Figra2406/Grupo-1-FunBio/Documentos/Entregable 8/Entregable N°8.pdf

### FUNDAMENTOS DE BIODISEÑO

Entrega N°8:
Diseño esquemático del prototipo. Modelado 3D de los elementos que conforman el prototipo

Grupo 1

Integrantes:
Fabrizzio Marcel Céliz Gálvez Jhogger Cercado Limay
Ximena Gema Palomino Cusi
Flavia Sharick Tasayco Cueva Javier Denis Bernal Garayar Lucero Rubi Cercado Medina 26/05/26

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
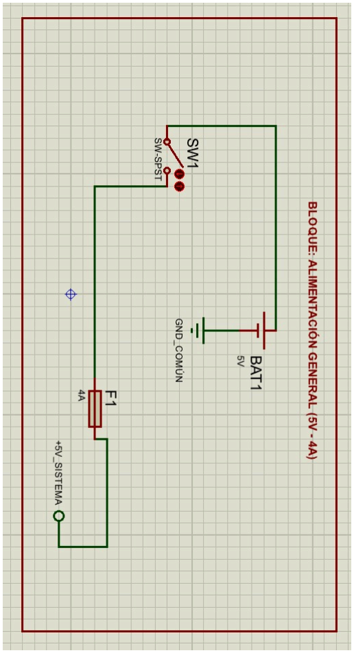
[picture p11: figure]
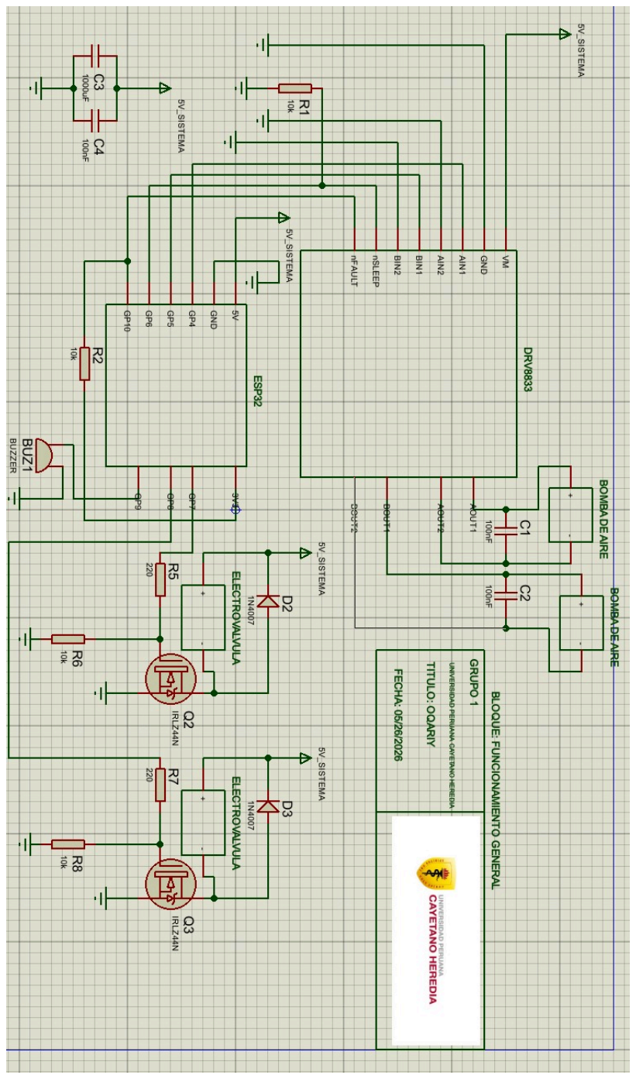
[picture p12: page 3]

- Modelado 3D de los componentes por separado

Enlace:
https://cad.onshape.com/documents/be2a5b314c4f87f89ed8f853/w/25158f458f5c1d92be45dfe7/e/40a314e245f769cd47d0e264 (https://cad.onshape.com/documents/be2a5b314c4f87f89ed8f853/w/25158f458f5c1d92be45dfe7/e/40a314e245f769cd47d0e264)
1. Bateria recargable 6v 3000mA
2. ESP32

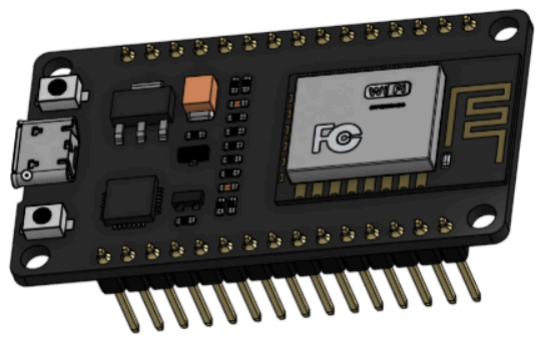
[picture p13: figure]

3. Mini bomba de aire 6V

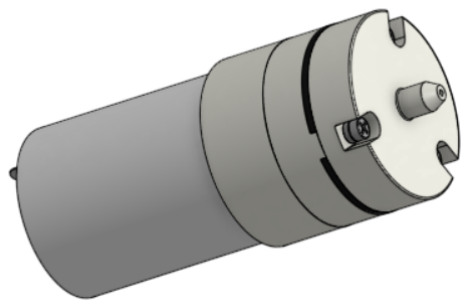
[picture p14: figure]

4. Micro valvula solenoide electrica

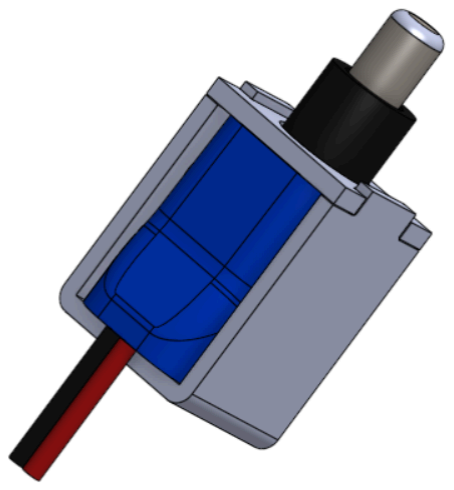
[picture p15: figure]

5. DRV8833

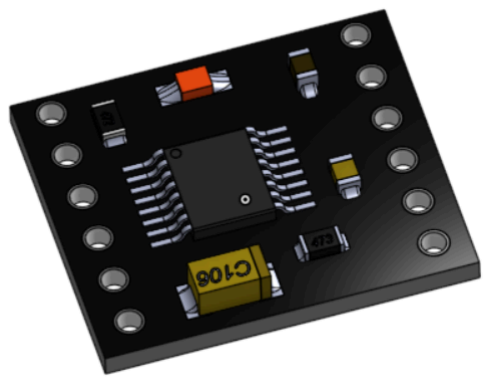
[picture p16: figure]

6. Transistor electronico MOSFET

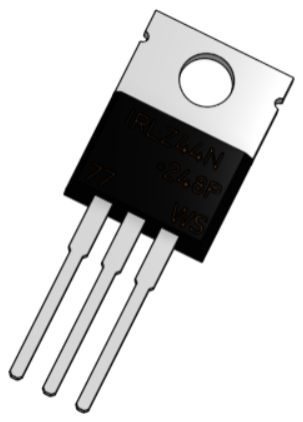
[picture p17: figure]

7. Buzzer

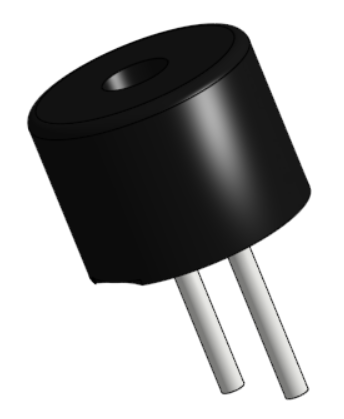
[picture p18: figure]

8. Bolsa de aire

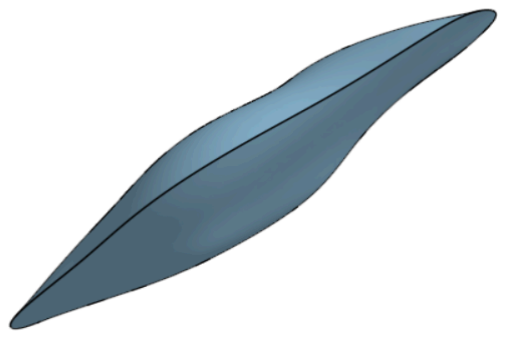
[picture p19: figure]

9. Soporte de elevación

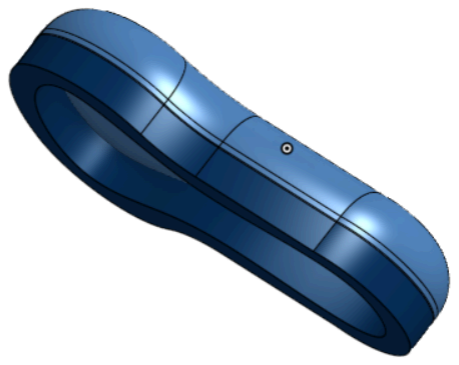
[picture p20: figure]
