Figra2406/Grupo-1-FunBio/Taller de modelado 3D/Lucero Cercado Medina/lucero-rubi-cercado-medina-7954d3f0-f888-4501-aeab-b428a17639e1-certificate.pdf

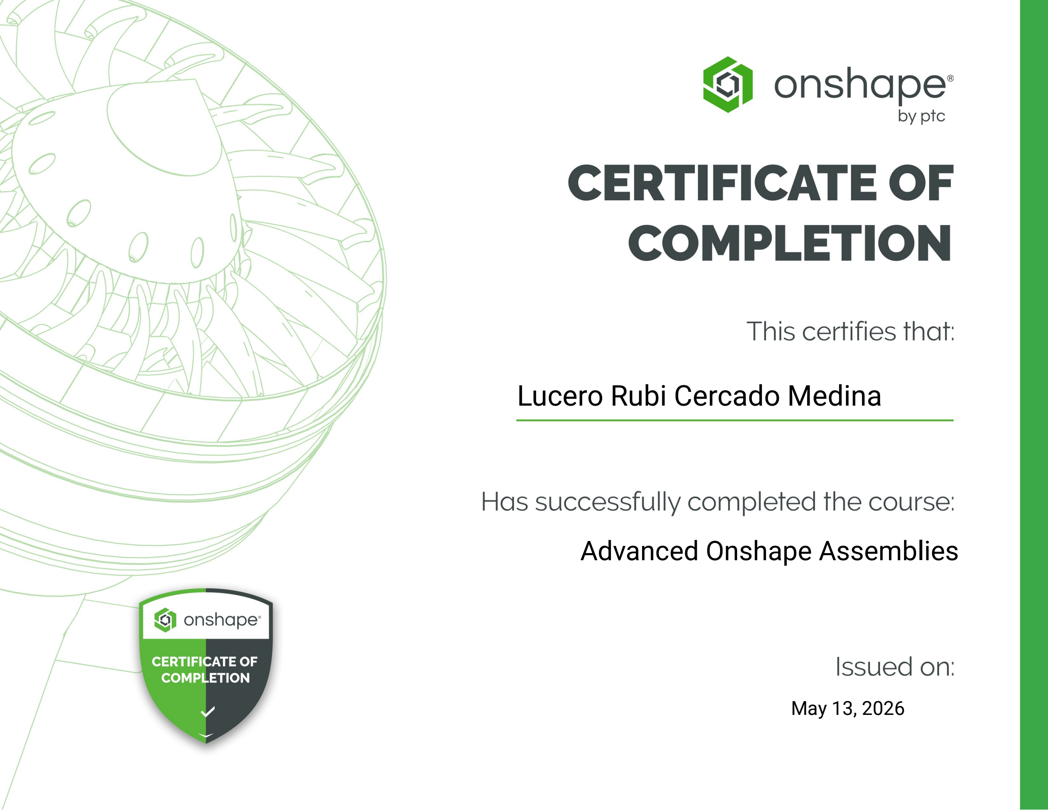
[picture p21: page 1]

Lucero Rubi Cercado Medina

Advanced Onshape Assemblies

May 13, 2026
