Figra2406/Grupo-1-FunBio/Taller de modelado 3D/Javier Bernal Garay/javier-bernal-1c711cbe-b023-4eb5-af85-3679d9fcc2b4-certificate.pdf

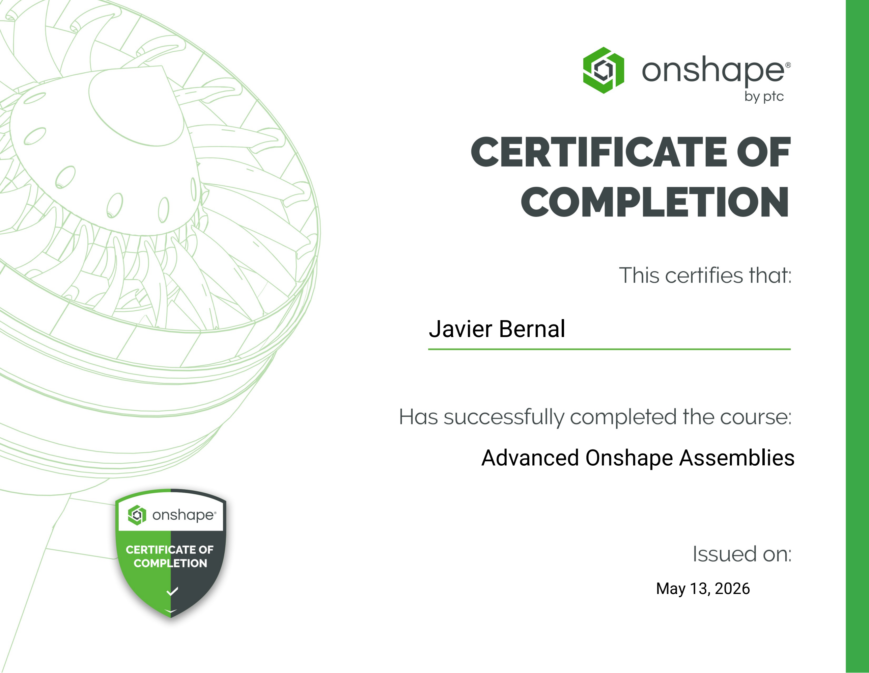
[picture p22: page 1]

Javier Bernal

Advanced Onshape Assemblies

May 13, 2026
