Figra2406/Grupo-1-FunBio/Taller de modelado 3D/Javier Bernal Garay/javier-bernal-4c75c975-a74c-4049-8172-a8e1c8366483-certificate.pdf

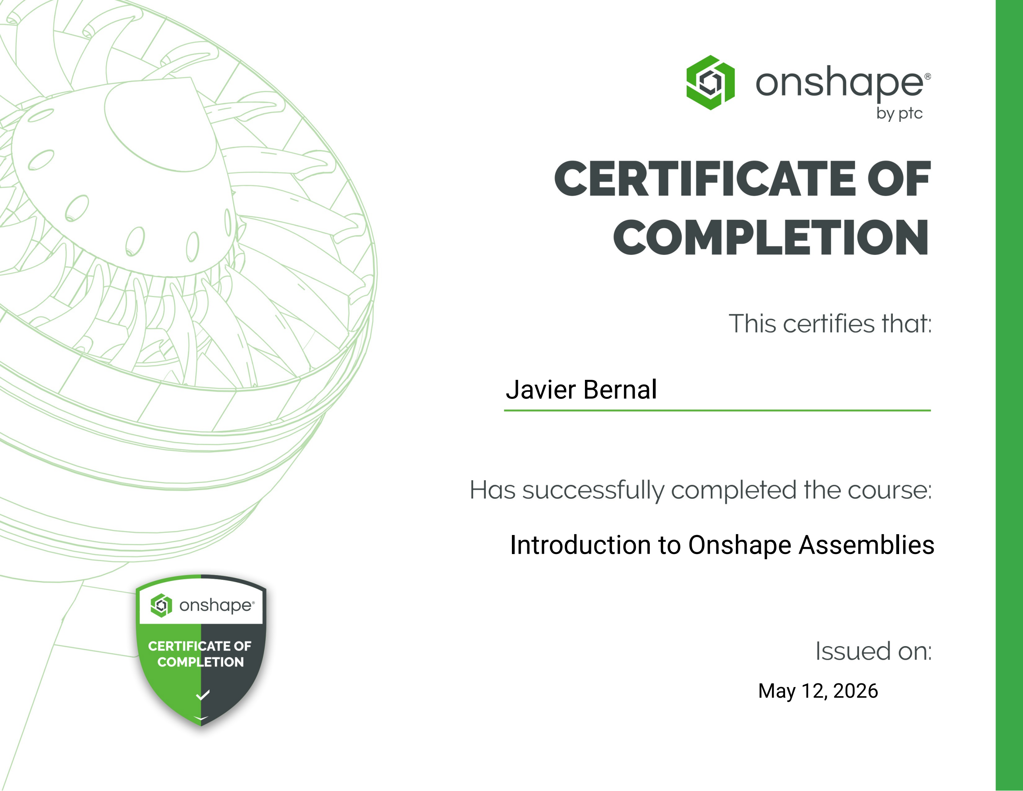
[picture p23: page 1]

Javier Bernal

May 12, 2026

Introduction to Onshape Assemblies
