Figra2406/Grupo-1-FunBio/Taller de modelado 3D/Lucero Cercado Medina/de60d86d-8ce0-4c51-bb0f-3838b6e36f22-lucero-rubi-cercado-medina-431d9740-cd10-450a-8145-1995c47c14eb-certificate.pdf

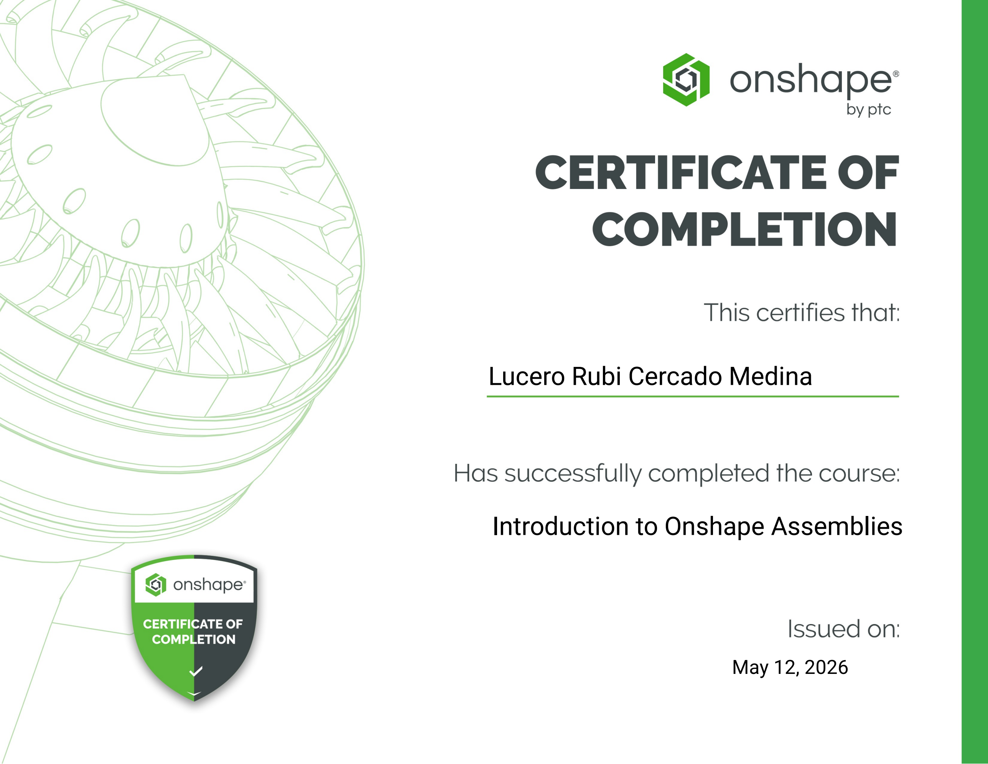
[picture p24: page 1]

Lucero Rubi Cercado Medina

May 12, 2026

Introduction to Onshape Assemblies
