Figra2406/Grupo-1-FunBio/Taller de modelado 3D/Ximena Palomino Cusi/gema-palomino-905db795-45b4-4cf6-ba11-d0b69c7ab82a-certificate.pdf

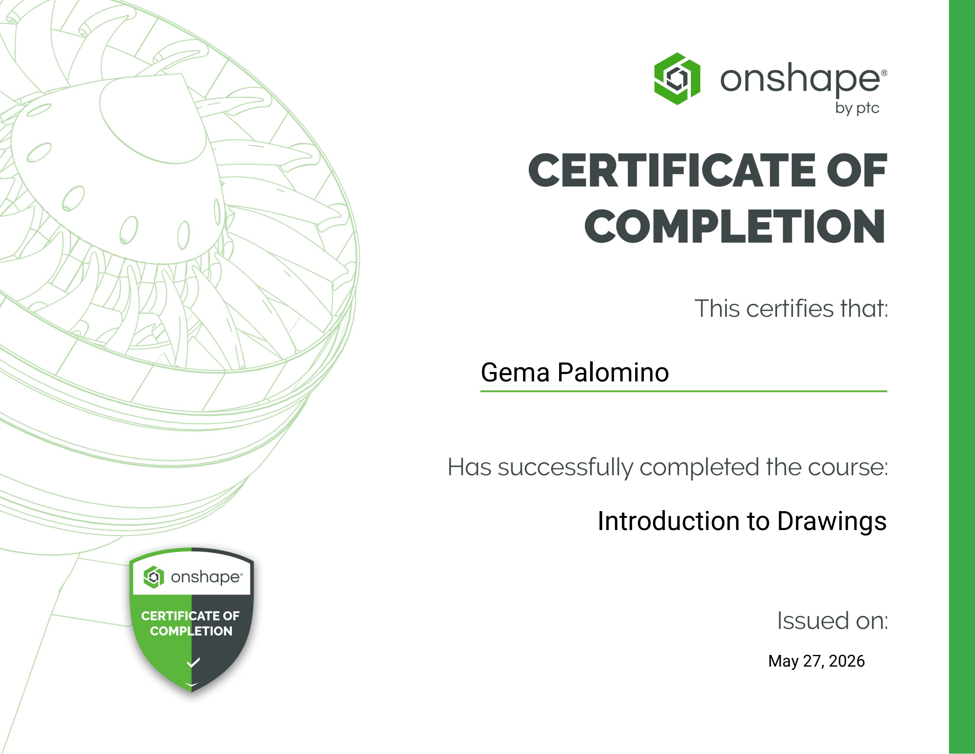
[picture p25: page 1]

Gema Palomino

May 27, 2026

Introduction to Drawings
