Figra2406/Grupo-1-FunBio/Taller de modelado 3D/Flavia Tasayco Cueva/Detailed Drawings.pdf

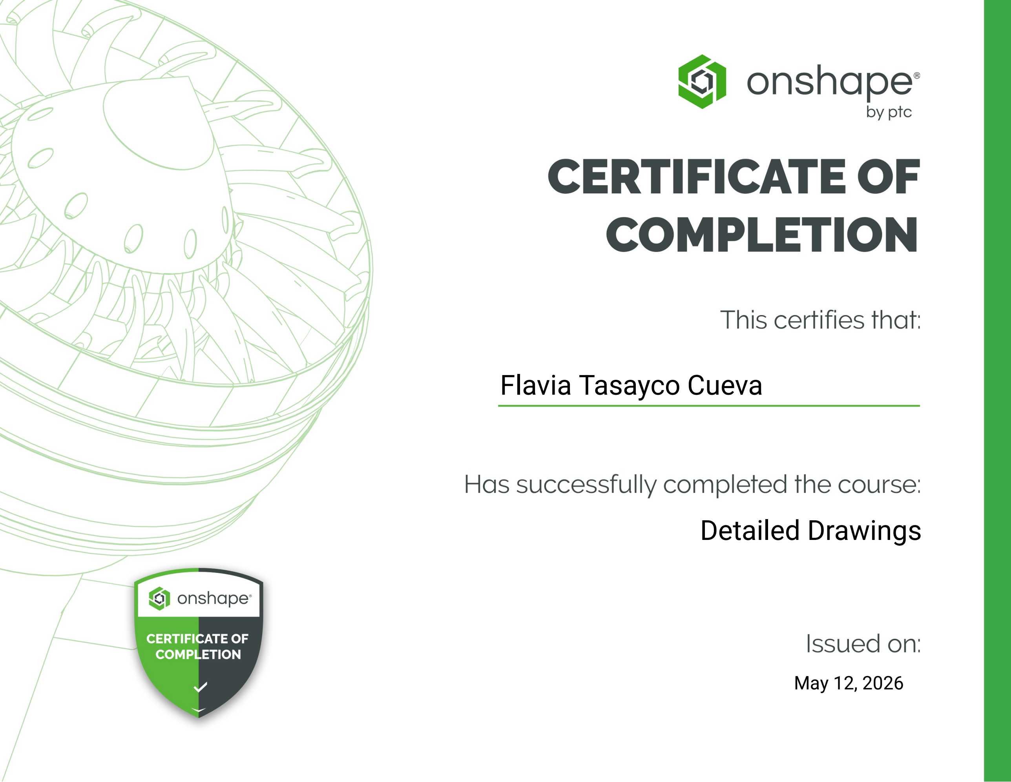
[picture p26: page 1]

Flavia Tasayco Cueva

May 12, 2026

Detailed Drawings
