Figra2406/Grupo-1-FunBio/Taller de modelado 3D/Javier Bernal Garay/javier-bernal-8e3854ba-d66e-4511-bbd3-1ceb8dc3e522-certificate.pdf

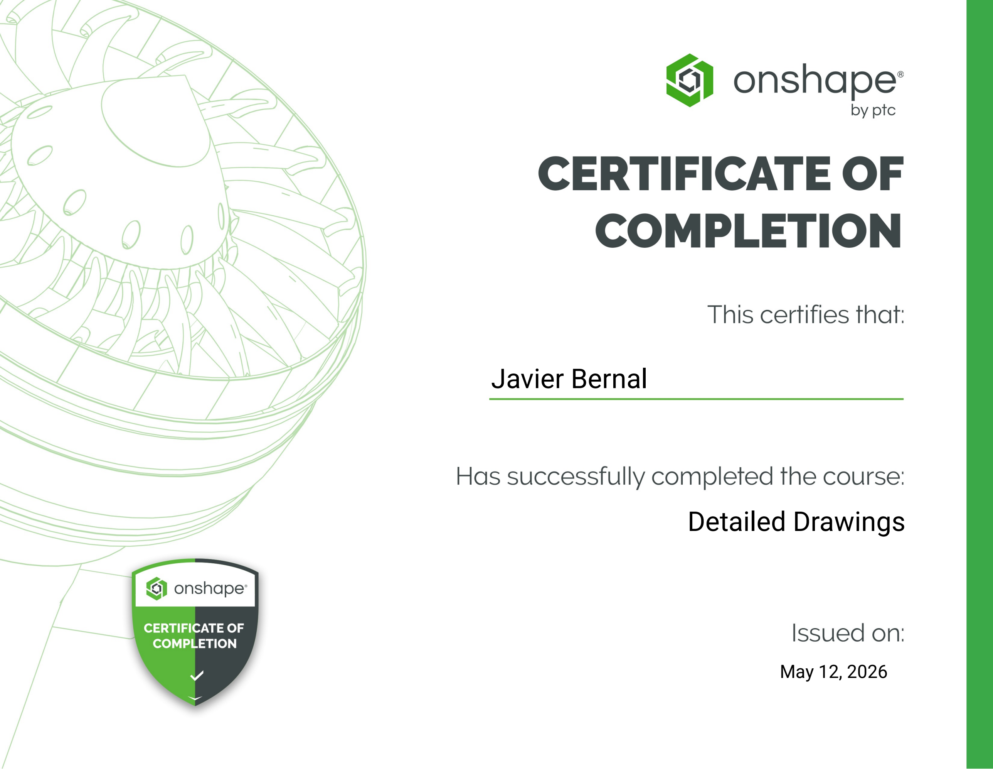
[picture p27: page 1]

Javier Bernal

May 12, 2026

Detailed Drawings
