Figra2406/Grupo-1-FunBio/Taller de modelado 3D/Lucero Cercado Medina/de60d86d-8ce0-4c51-bb0f-3838b6e36f22-lucero-rubi-cercado-medina-5331641c-7917-43de-a894-fe1695d6f287-certificate.pdf

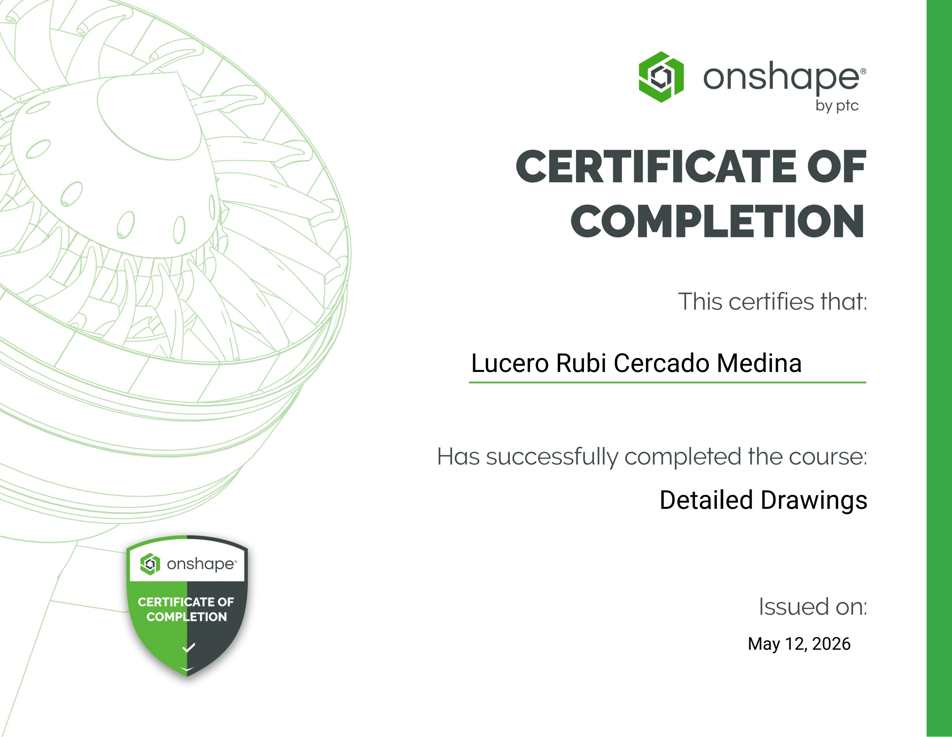
[picture p28: page 1]

Lucero Rubi Cercado Medina

May 12, 2026

Detailed Drawings
