Figra2406/Grupo-1-FunBio/Taller de modelado 3D/Ximena Palomino Cusi/Detailed Drawings.pdf

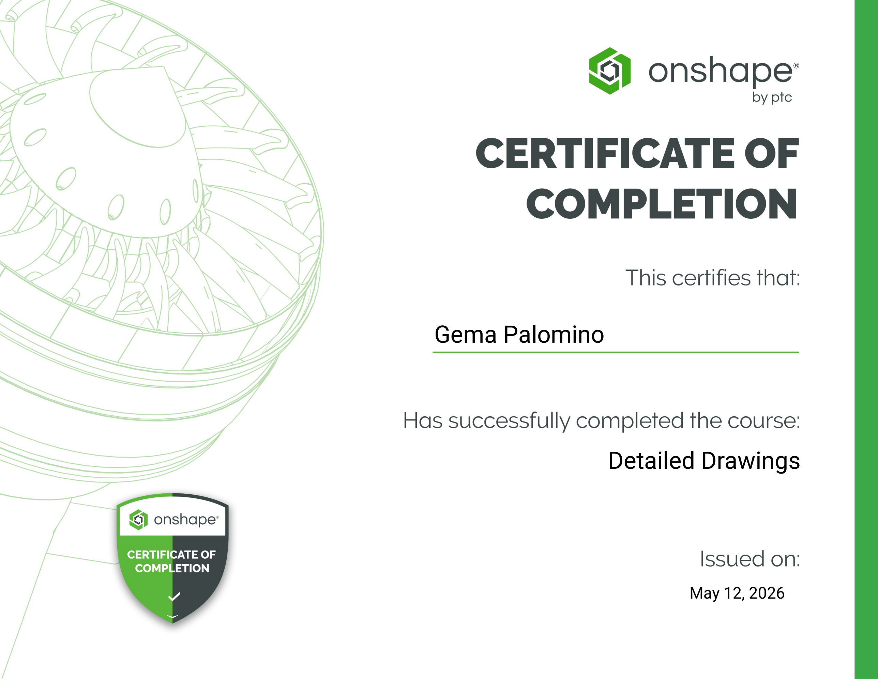
[picture p29: page 1]

Gema Palomino

May 12, 2026

Detailed Drawings
