Figra2406/Grupo-1-FunBio/Taller de modelado 3D/Javier Bernal Garay/javier-bernal-89edafed-4be2-4a4e-a87d-024590466d2e-certificate.pdf

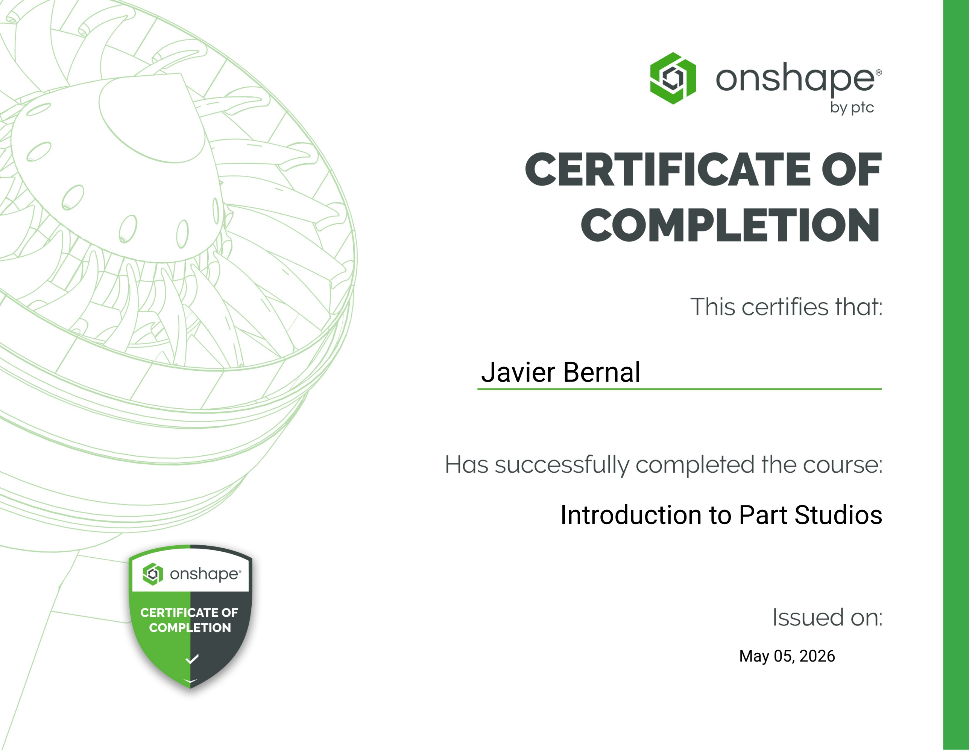
[picture p36: page 1]

Javier Bernal

Introduction to Part Studios

May 05, 2026
