Figra2406/Grupo-1-FunBio/Taller de modelado 3D/Javier Bernal Garay/javier-bernal-d9db2dbc-3374-4bca-a5cd-d3212916cf07-certificate.pdf

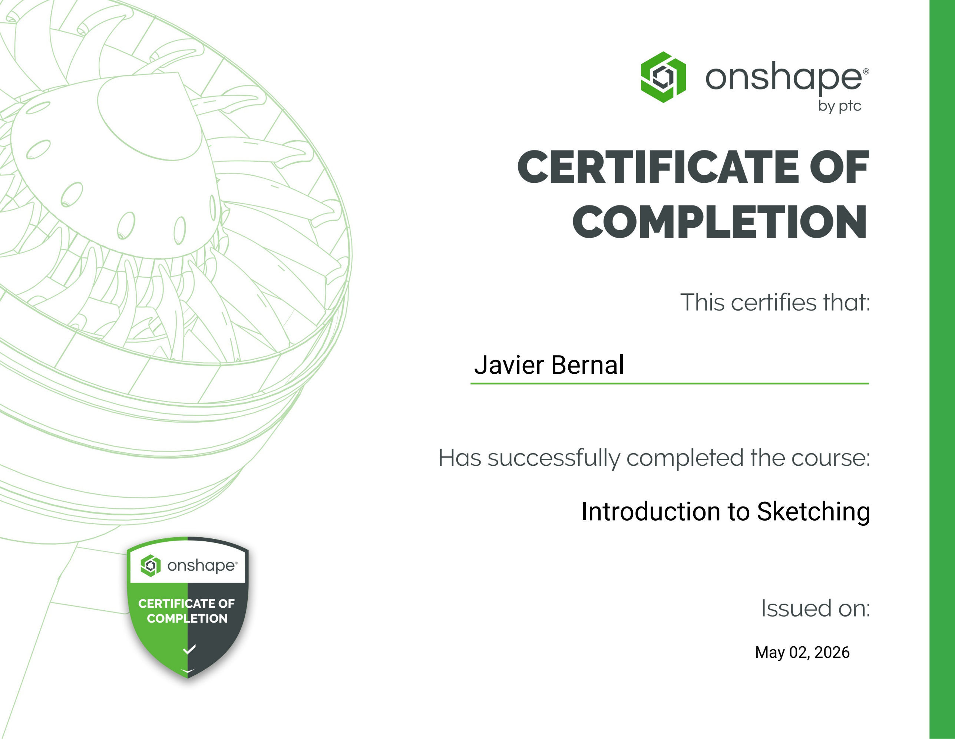
[picture p37: page 1]

Javier Bernal

Introduction to Sketching

May 02, 2026
