Figra2406/Grupo-1-FunBio/Taller de modelado 3D/Flavia Tasayco Cueva/Introduction to Part Studios.Flavia.pdf

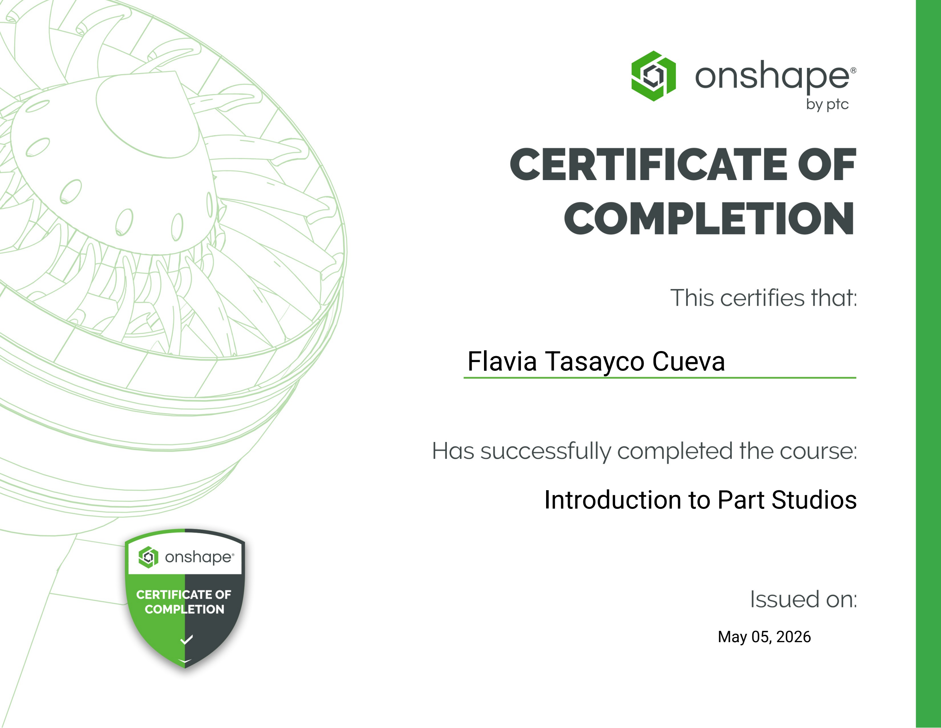
[picture p38: page 1]

Flavia Tasayco Cueva

Introduction to Part Studios

May 05, 2026
