Figra2406/Grupo-1-FunBio/Taller de modelado 3D/Flavia Tasayco Cueva/Introduction to sketching.Flavia.pdf

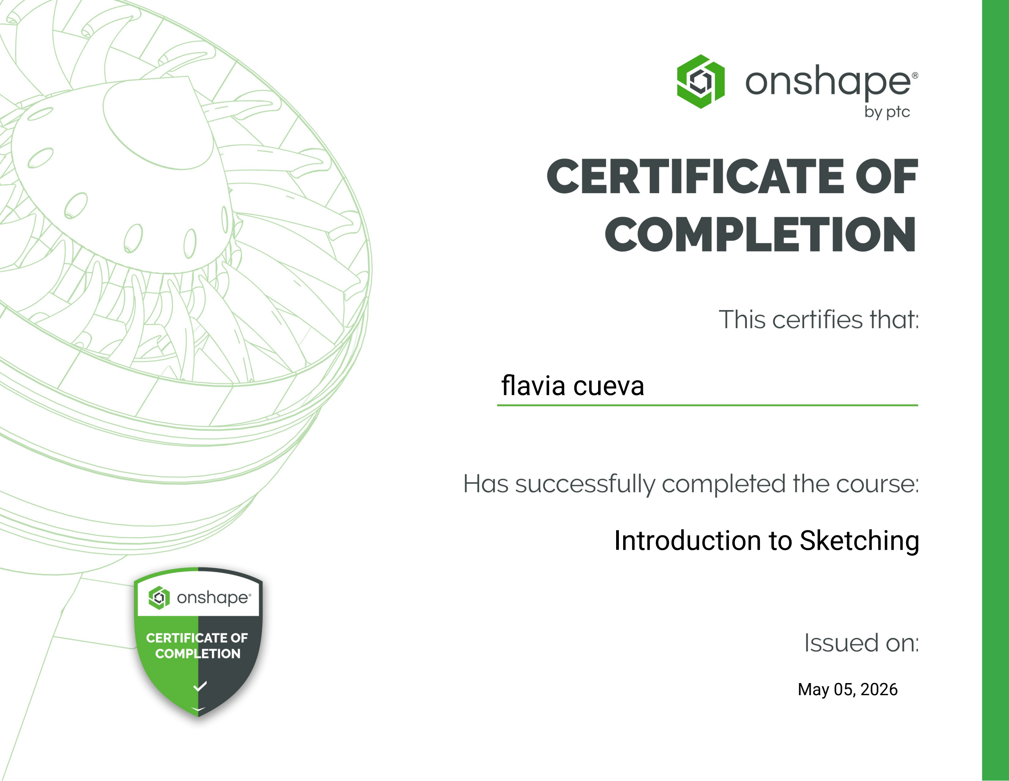
[picture p39: page 1]

avia cueva

Introduction to Sketching

May 05, 2026
