Figra2406/Grupo-1-FunBio/Taller de modelado 3D/Lucero Cercado Medina/lucero-rubi-cercado-medina-7111d44b-160b-4e92-bb52-a8f6cbea0b17-certificate.pdf

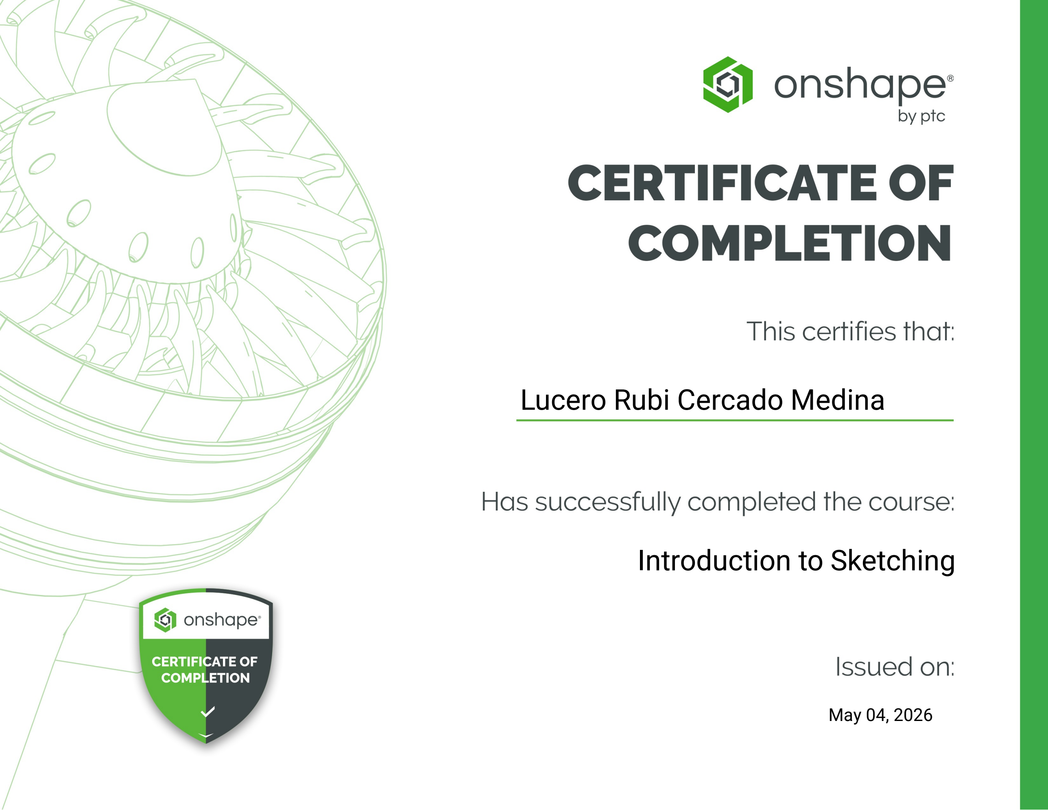
[picture p40: page 1]

Lucero Rubi Cercado Medina

Introduction to Sketching

May 04, 2026
