Figra2406/Grupo-1-FunBio/Taller de modelado 3D/Lucero Cercado Medina/lucero-rubi-cercado-medina-b66944c8-f012-4613-a5c3-b3f6f3d40ffe-certificate.pdf

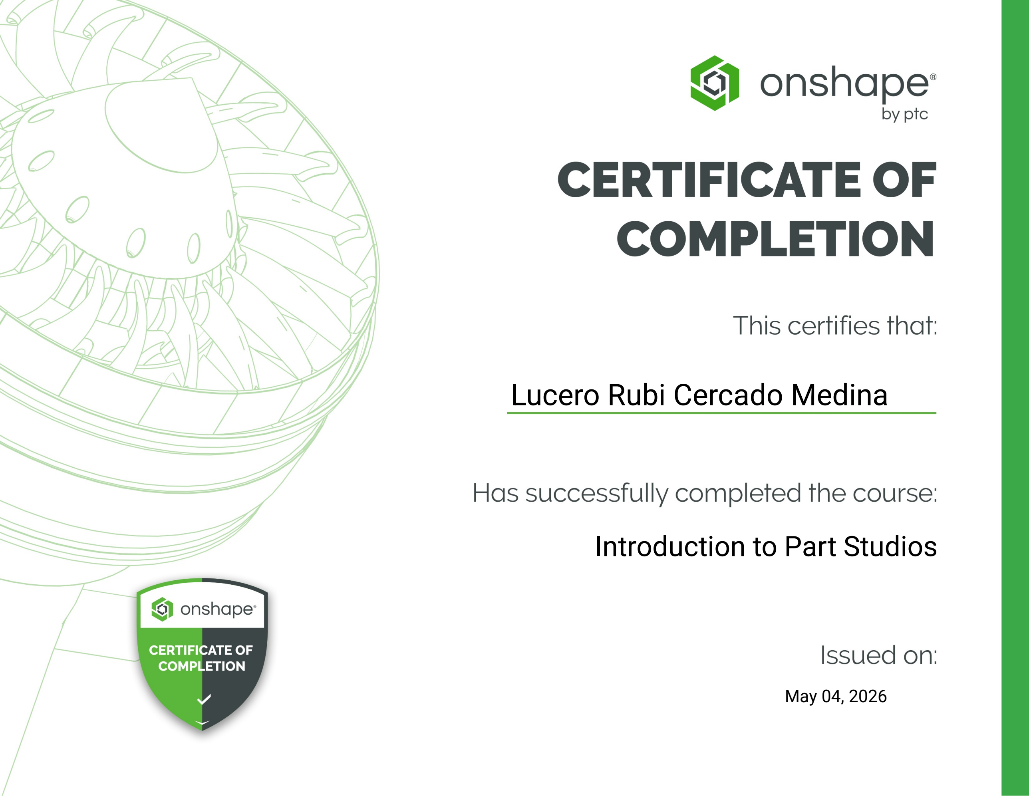
[picture p41: page 1]

Lucero Rubi Cercado Medina

Introduction to Part Studios

May 04, 2026
