Figra2406/Grupo-1-FunBio/Taller de modelado 3D/Ximena Palomino Cusi/Introduction to Part Studios.pdf

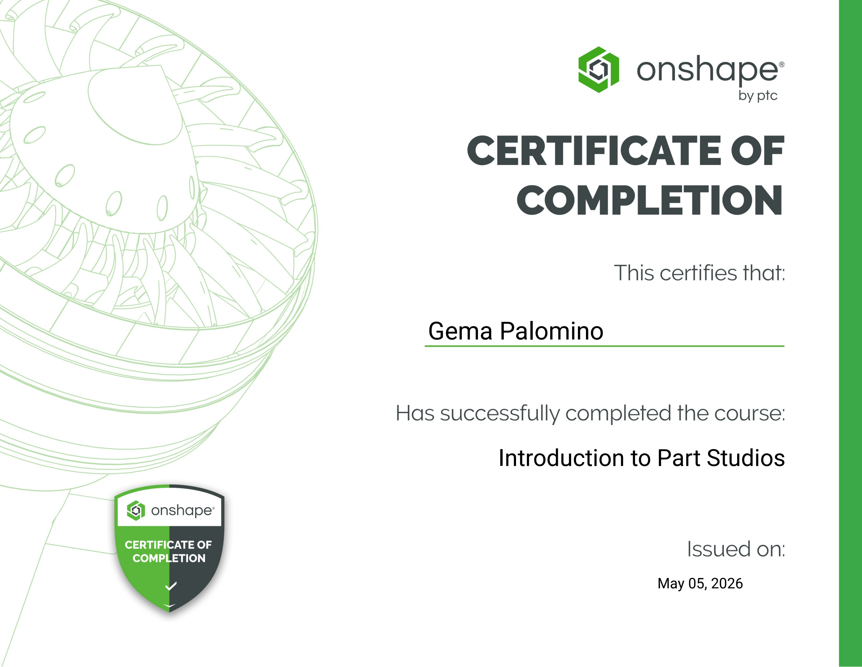
[picture p42: page 1]

Gema Palomino

Introduction to Part Studios

May 05, 2026
