Figra2406/Grupo-1-FunBio/Taller de modelado 3D/Ximena Palomino Cusi/Introducción al dibujo técnico.pdf

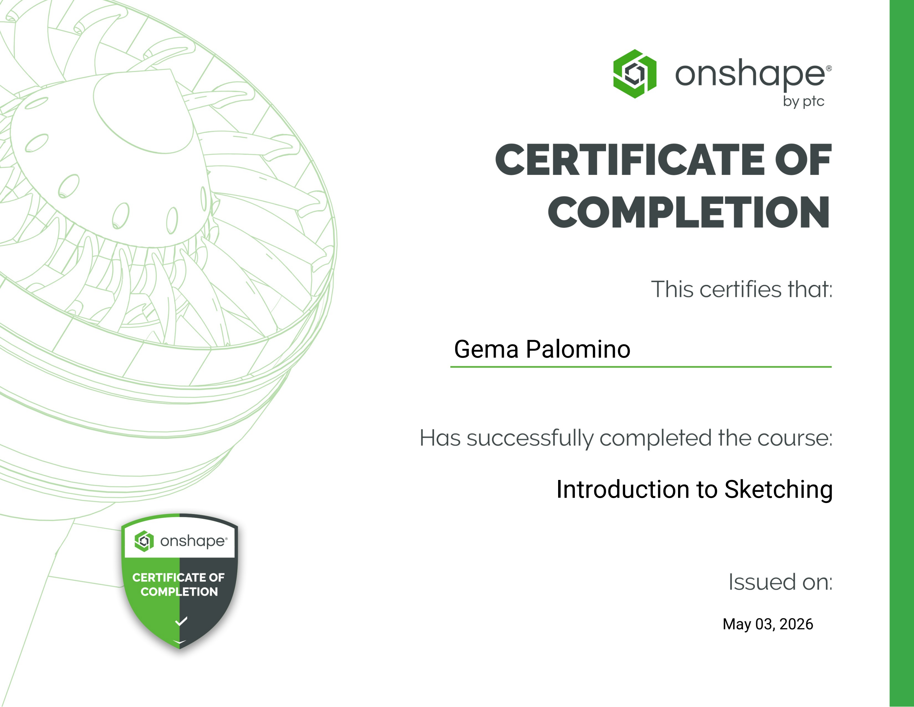
[picture p43: page 1]

Gema Palomino

Introduction to Sketching

May 03, 2026
