Figra2406/Grupo-1-FunBio/Taller de modelado 3D/Jhogger Cercado Limay/Dibujos detallados.pdf

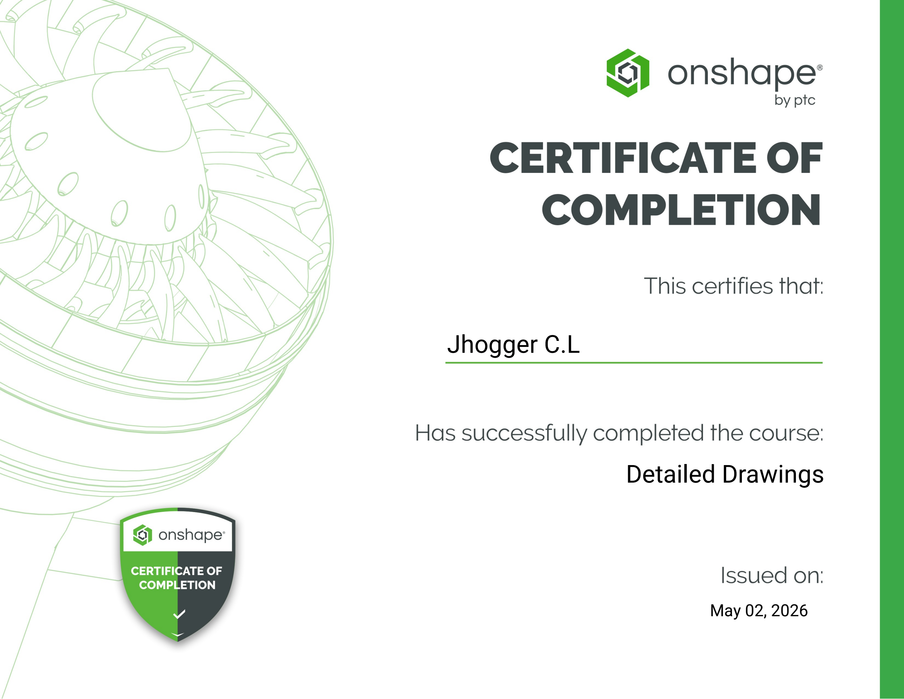
[picture p44: page 1]

Jhogger C.L

May 02, 2026

Detailed Drawings
