Figra2406/Grupo-1-FunBio/Taller de modelado 3D/Jhogger Cercado Limay/Introducción a Part Studios.pdf

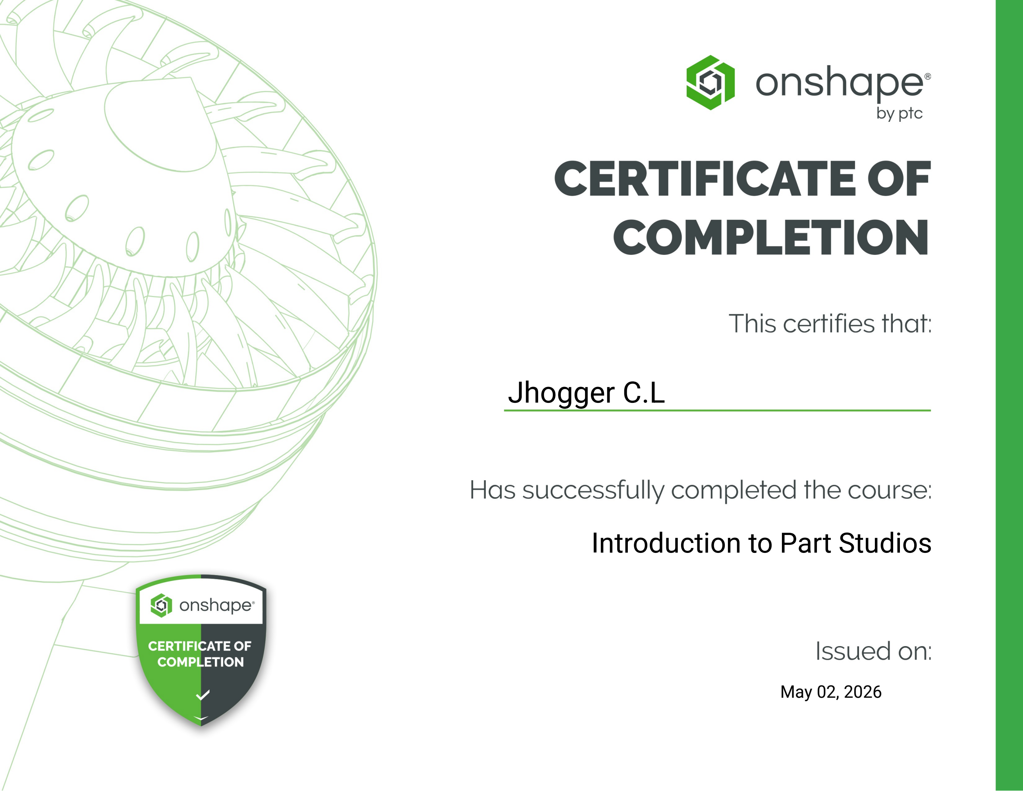
[picture p45: page 1]

Jhogger C.L

Introduction to Part Studios

May 02, 2026
