Figra2406/Grupo-1-FunBio/Taller de modelado 3D/Jhogger Cercado Limay/Introducción al dibujo técnico.pdf

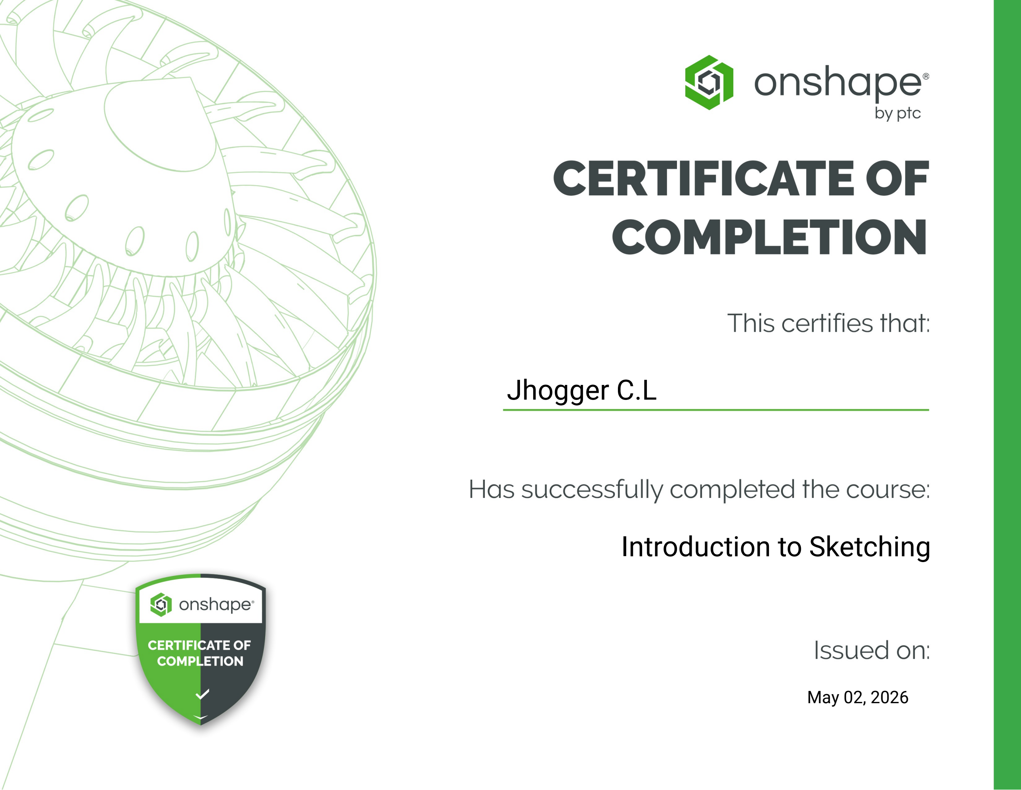
[picture p46: page 1]

Jhogger C.L

Introduction to Sketching

May 02, 2026
