Figra2406/Grupo-1-FunBio/Taller de modelado 3D/Fabrizzio Céliz Gálvez/Introducción a Part Studios Fabrizzio Céliz.pdf

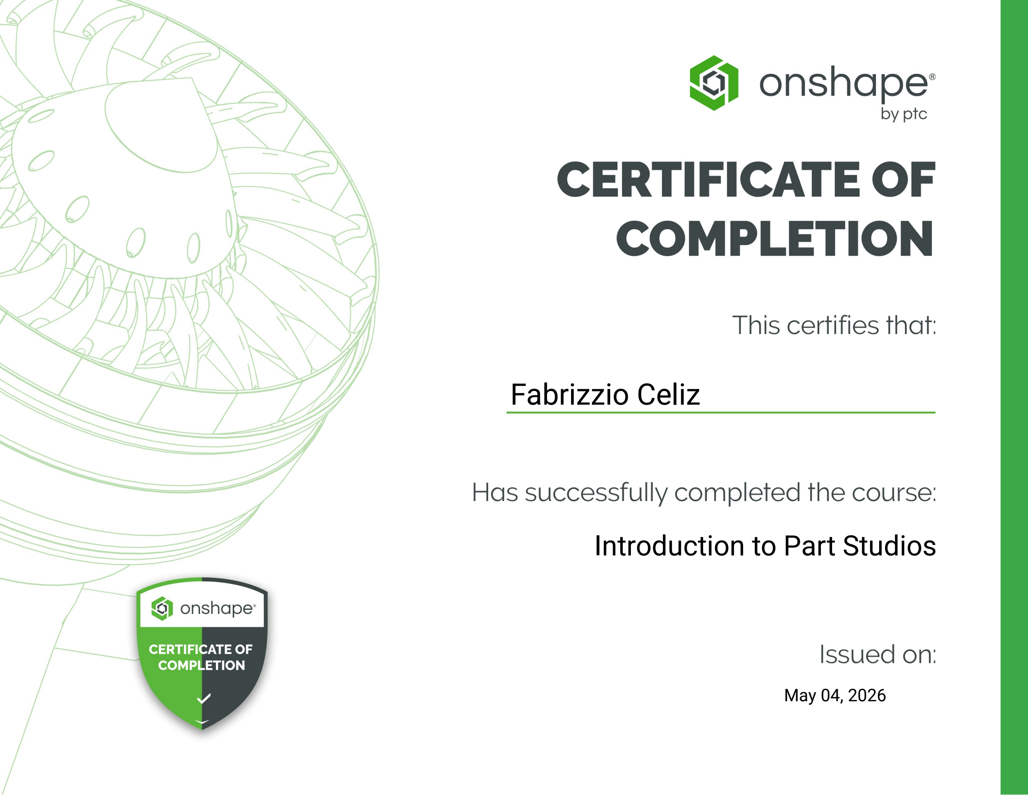
[picture p47: page 1]

Fabrizzio Celiz

Introduction to Part Studios

May 04, 2026
