Figra2406/Grupo-1-FunBio/Taller de modelado 3D/Fabrizzio Céliz Gálvez/Introducción al Dibujo Tecnico Fabrizzio Céliz.pdf

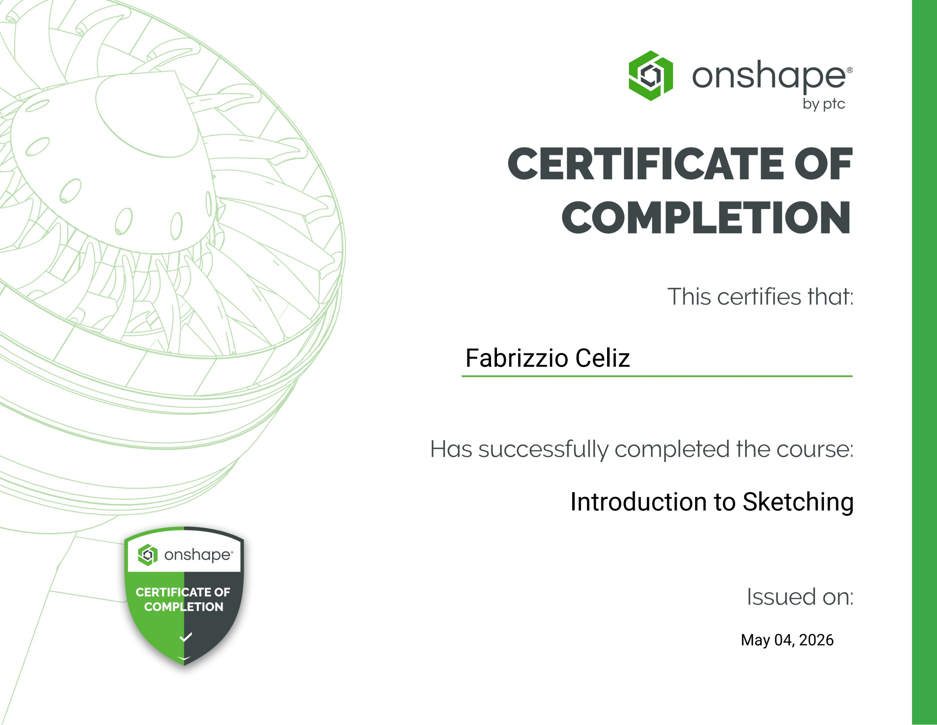
[picture p48: page 1]

Fabrizzio Celiz

Introduction to Sketching

May 04, 2026
