Figra2406/Grupo-1-FunBio/Imagenes/IMG_7878.jpeg

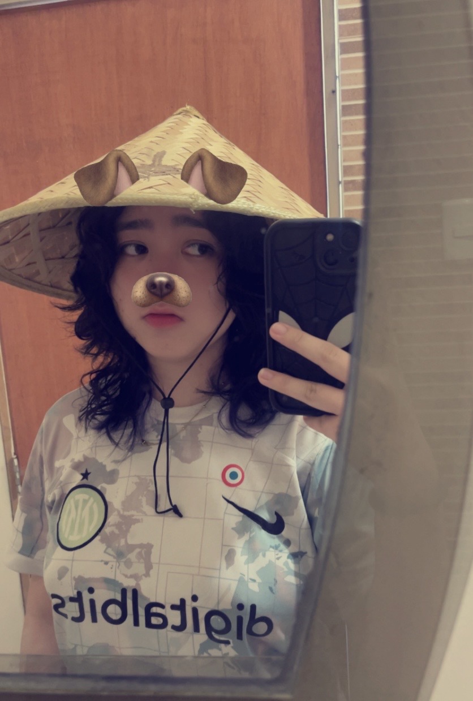
Imagenes/IMG_7878.jpeg
