Figra2406/Grupo-1-FunBio/Documentos/Entregable 9/Riñon plano.pdf

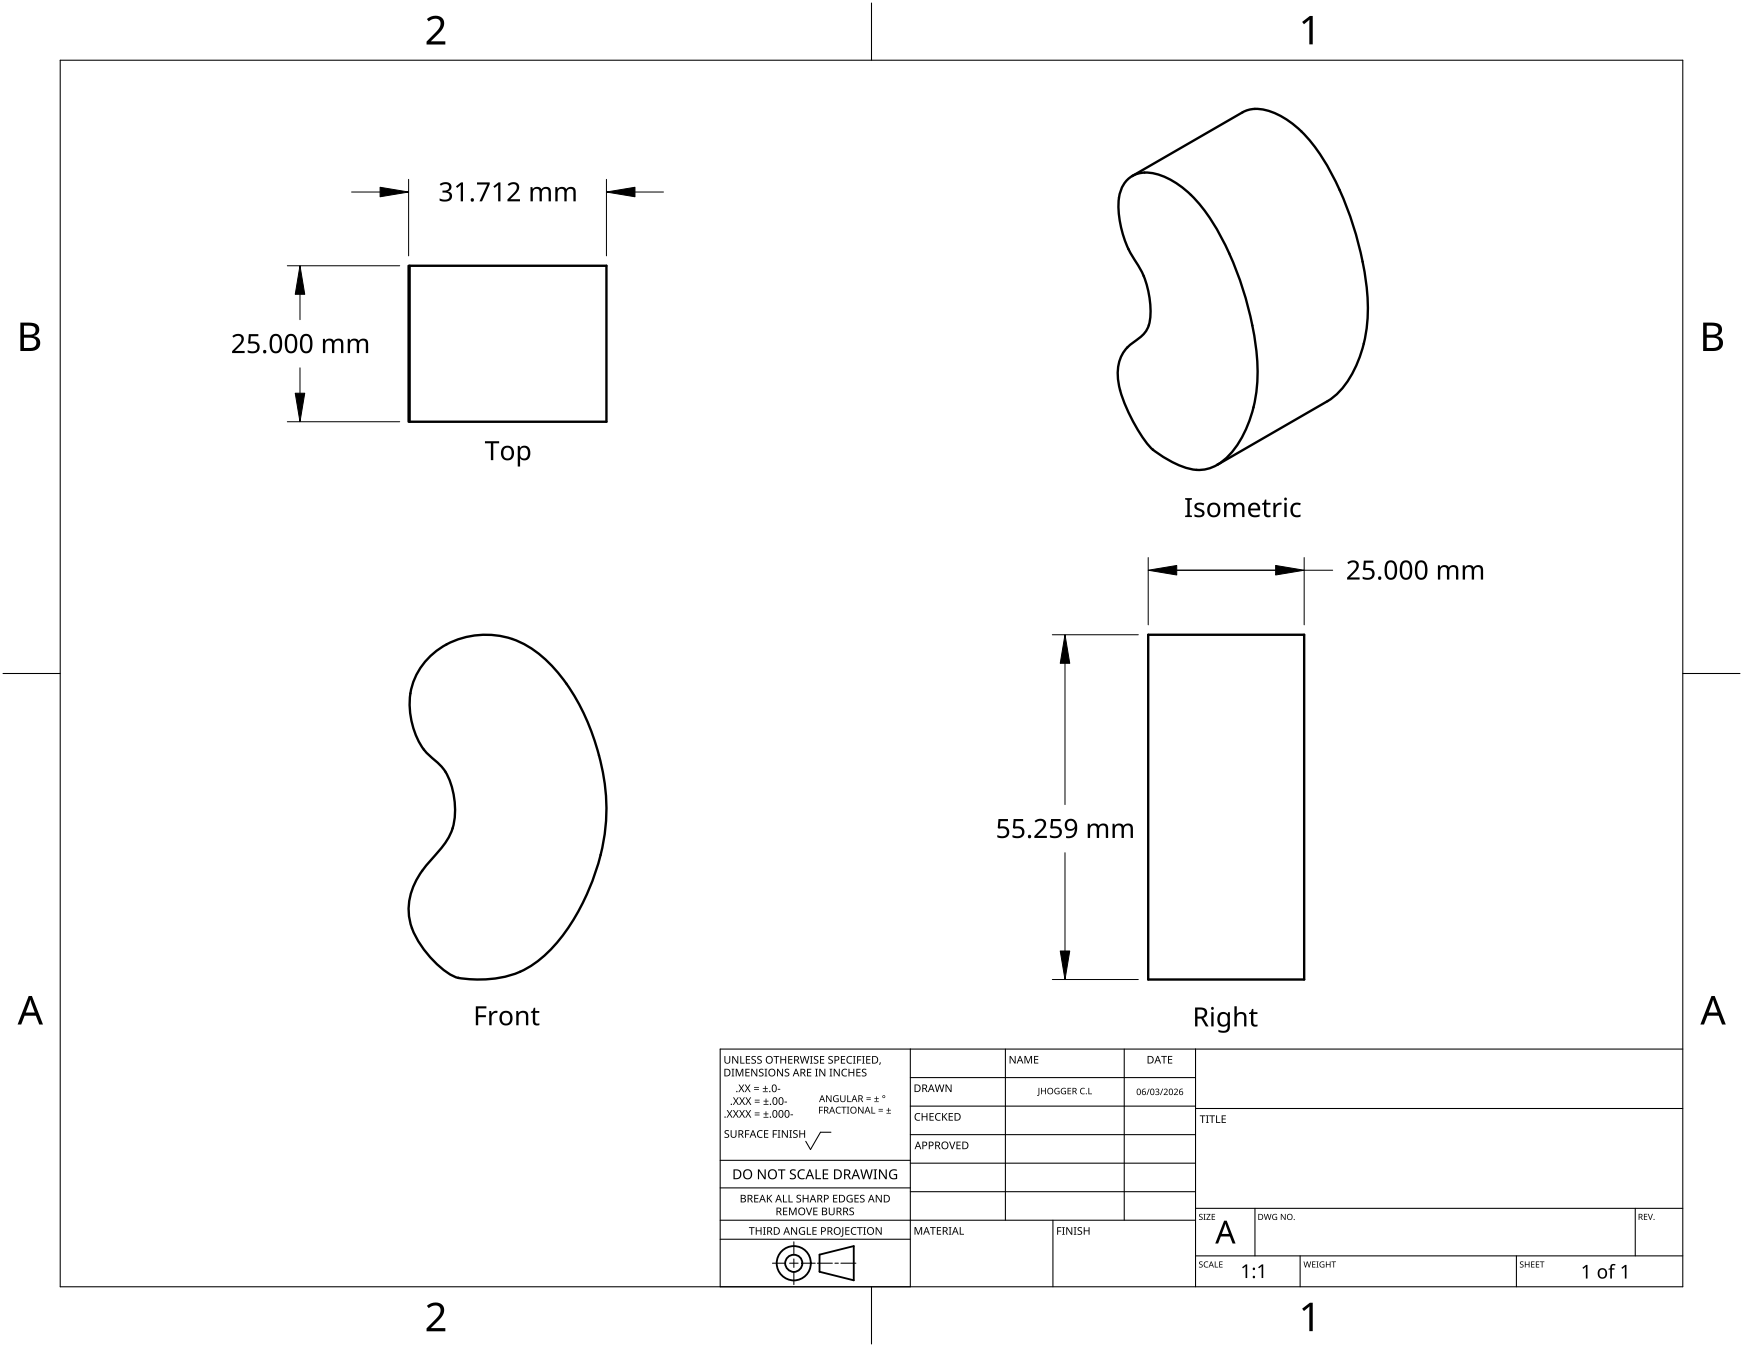
[picture p76: page 1]
