Figra2406/Grupo-1-FunBio/Documentos/Entregable 9/Tapa plano.pdf

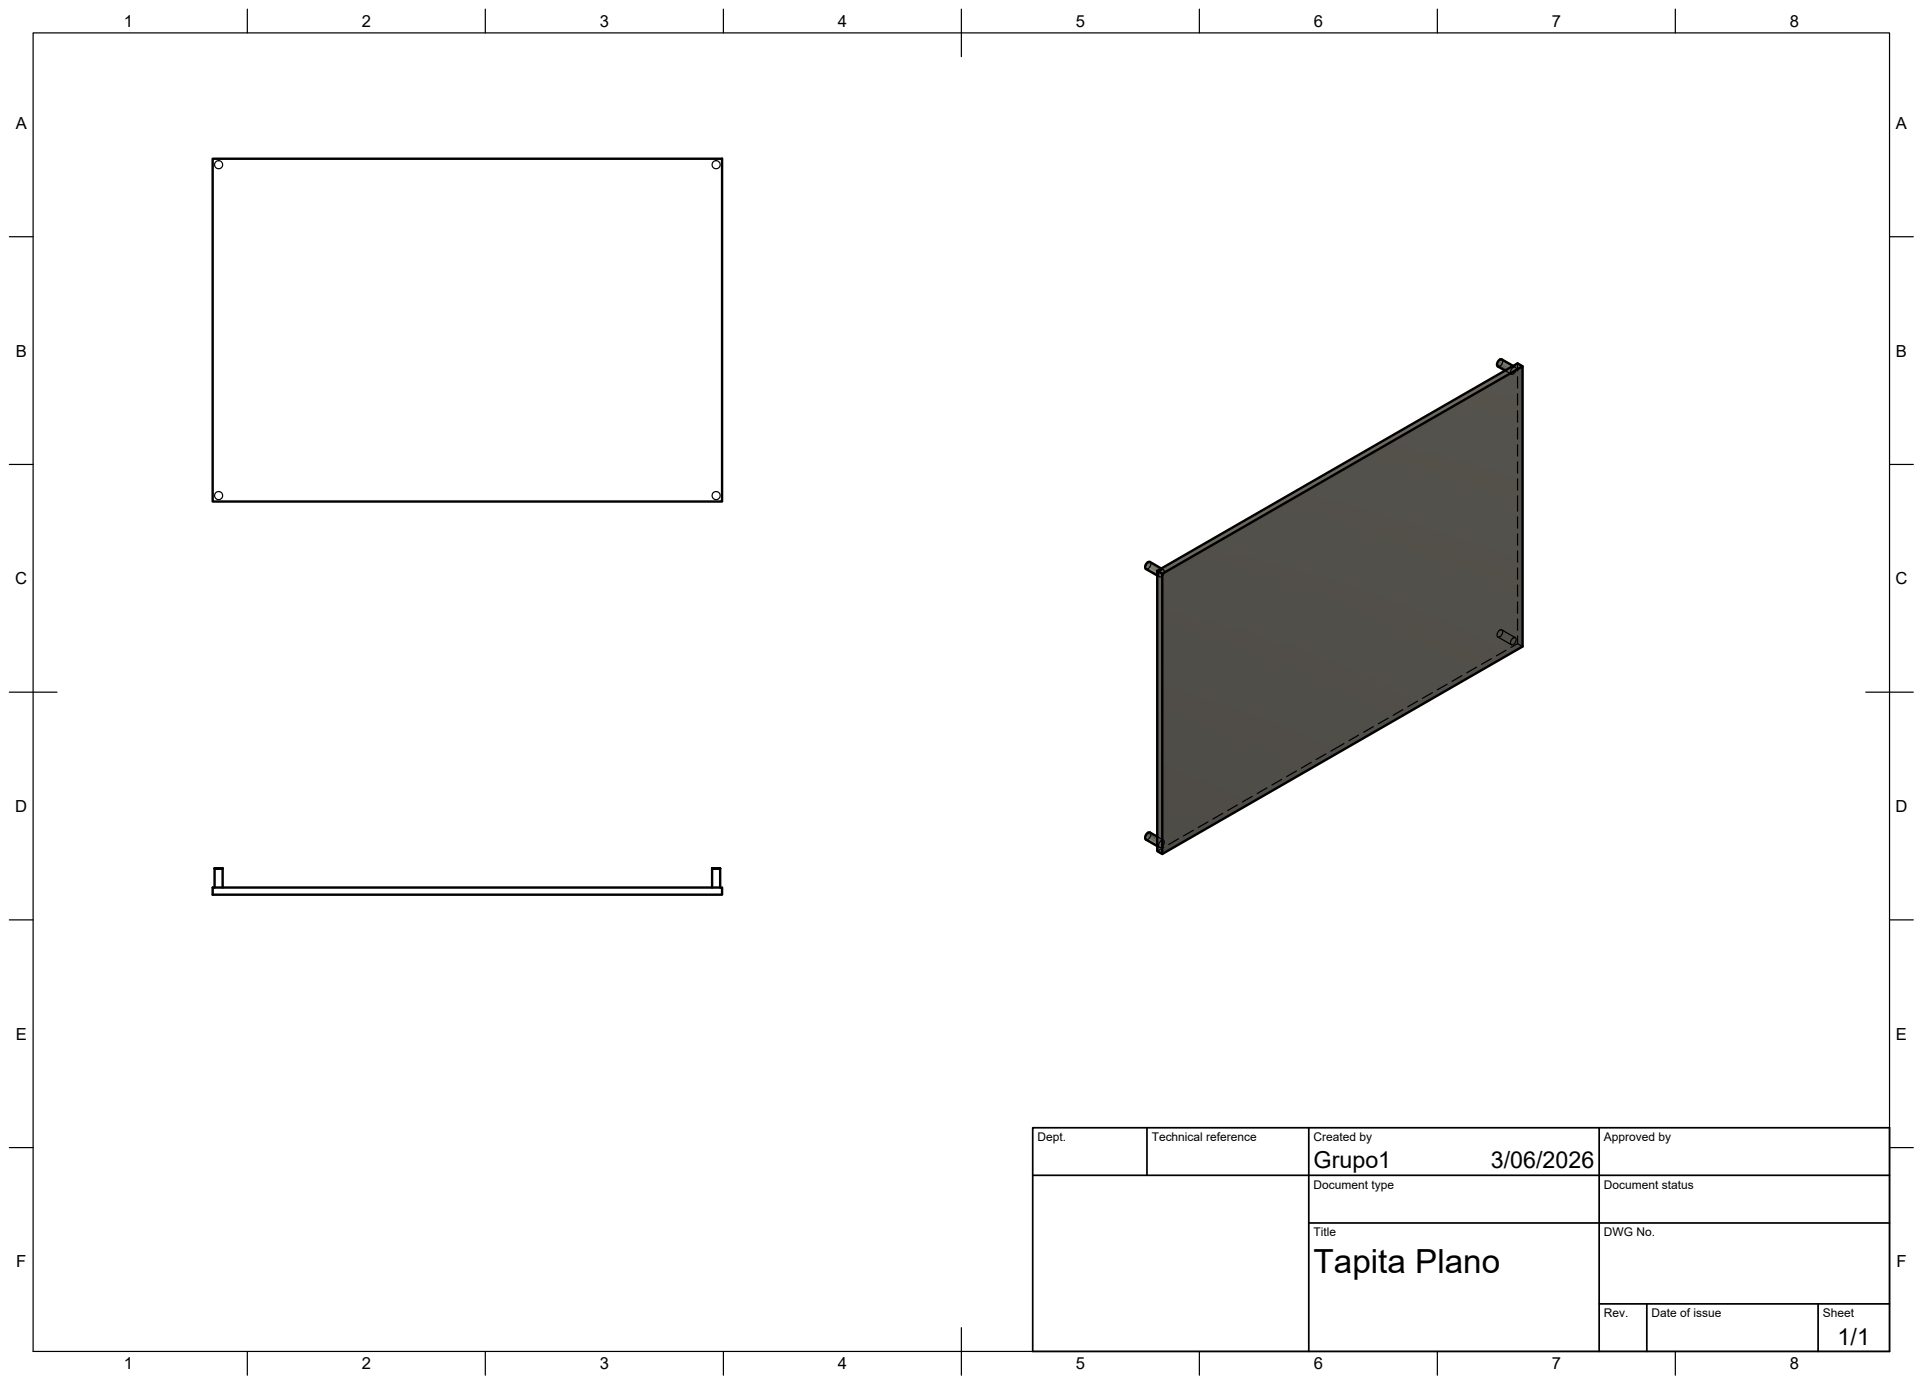
[picture p77: page 1]
Title; DWG No.; Rev.; Date of issue; Sheet; Tapita Plano

Dept. | Technical reference | Created by Grupo1 3/06/2026 | Approved by

Document type | Document status
