Figra2406/Grupo-1-FunBio/Documentos/Entregable 9/Caja plano.pdf

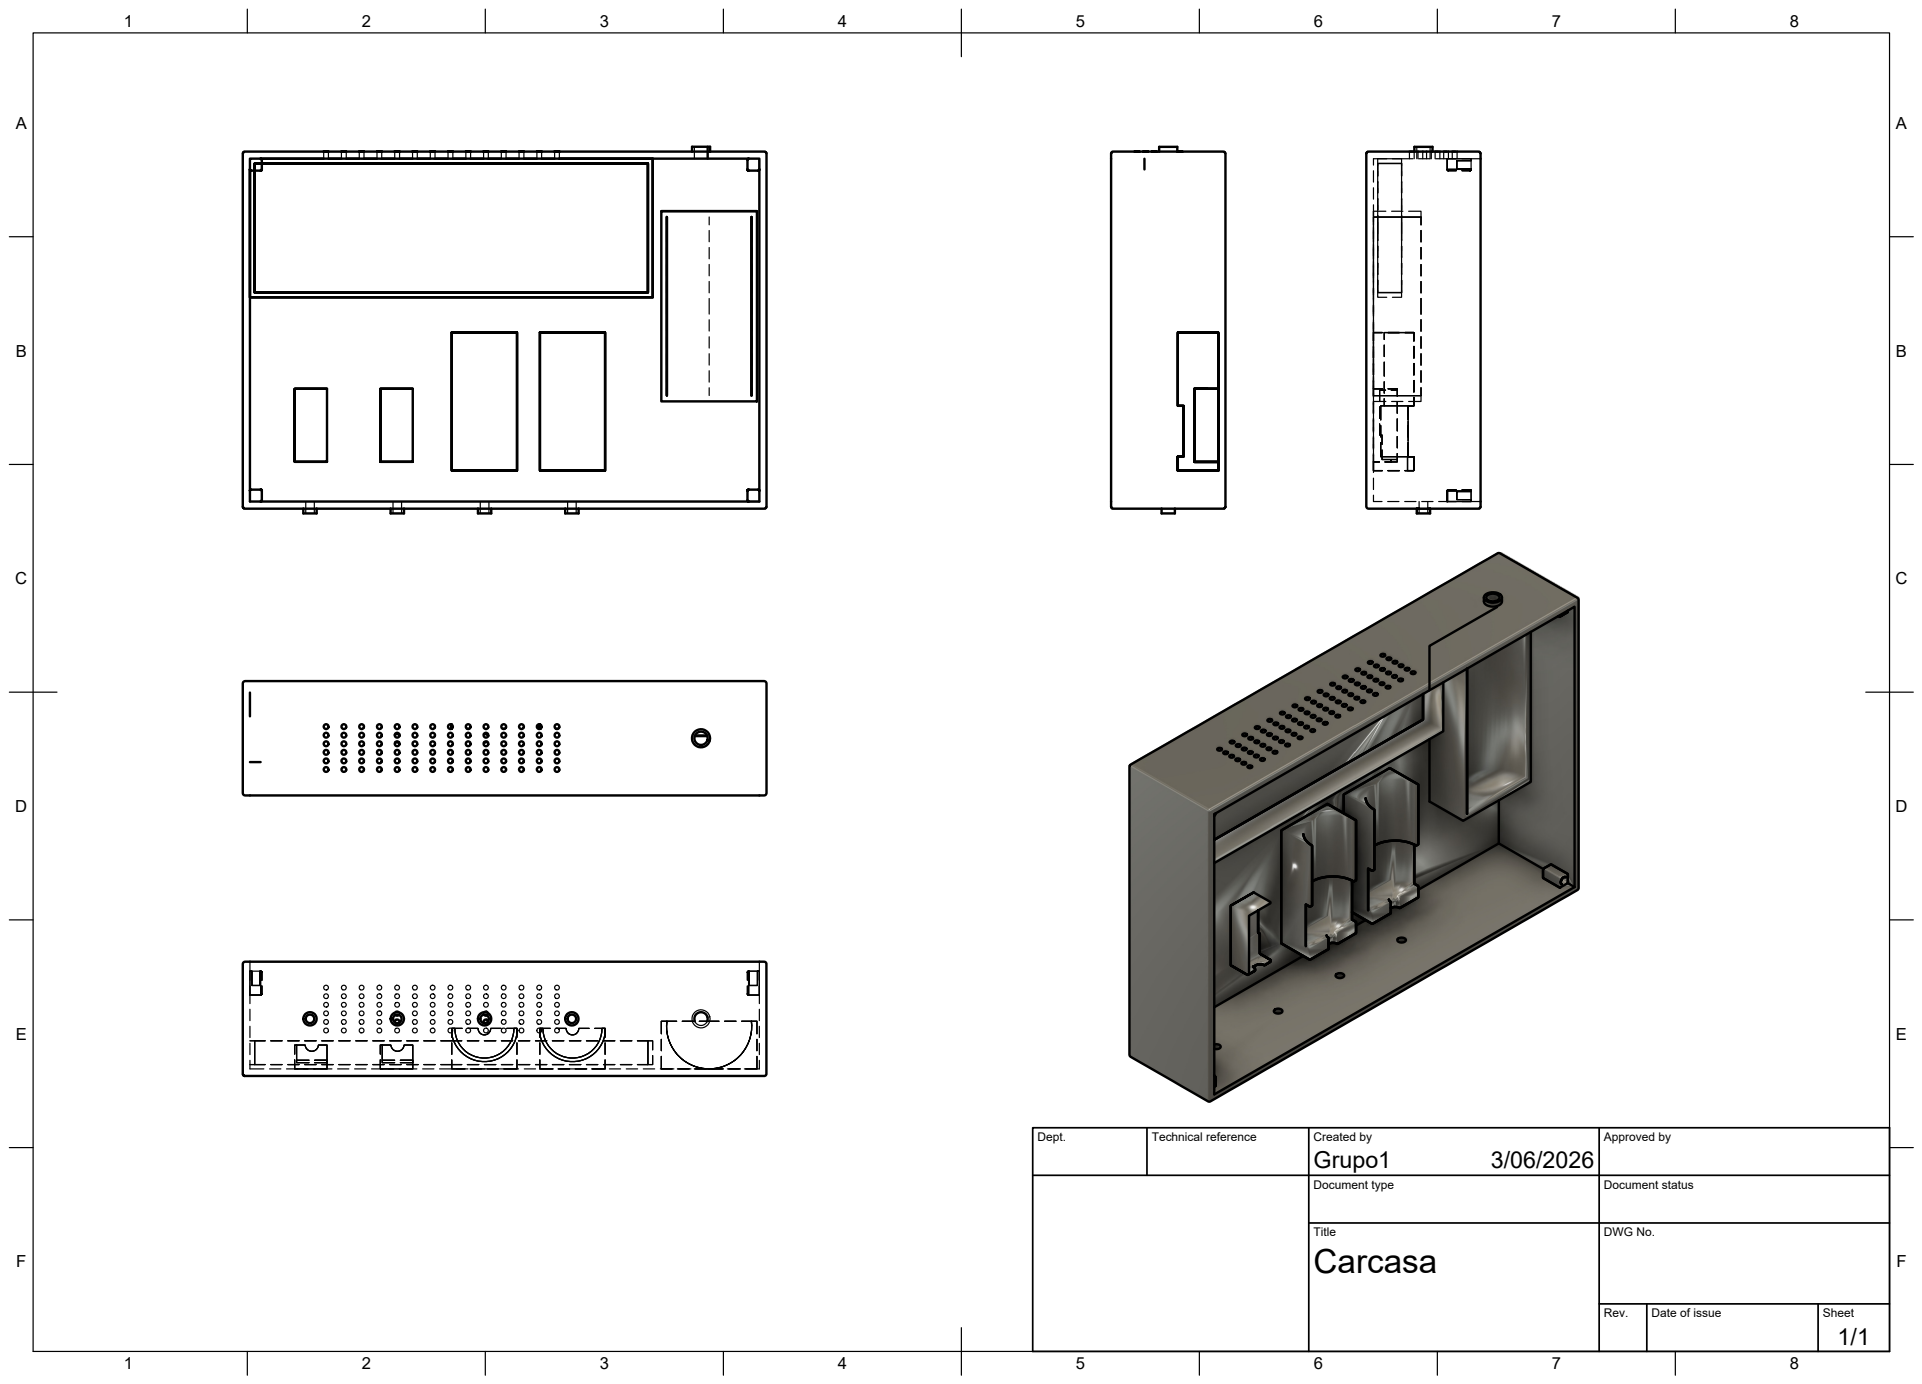
[picture p78: page 1]
Title; DWG No.; Rev.; Date of issue; Sheet

Dept. | Technical reference | Created by Grupo1 3/06/2026 | Approved by

Document type | Document status
